metaneutrons/Zorro-LAN-IDE/Driver/baxnet/source/version.h

/*
  version.h

  (C) 2018 Henryk Richter <henryk.richter@gmx.net>

  version and date handling
*/
#ifndef _INC_VERSION_H
#define _INC_VERSION_H

#define DEVICEVERSION  2
#define DEVICEREVISION 9
#define DEVICEEXTRA
/* #define DEVICEEXTRA Beta */
#define DEVICEDATE    23.08.20

#endif
